robertocarrascoso/TeaTouch-CFGB_Las_Naves_Salesianos/Branding/adsadasdsad.png

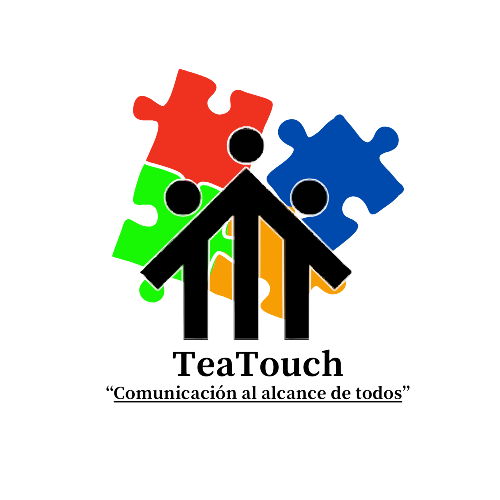
Branding/adsadasdsad.png
