robertocarrascoso/TeaTouch-CFGB_Las_Naves_Salesianos/Branding/asoc.-implica.jpg

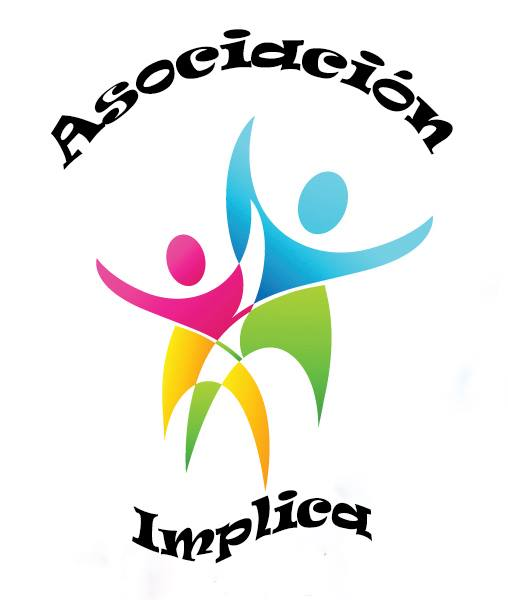
Branding/asoc.-implica.jpg
