robertocarrascoso/TeaTouch-CFGB_Las_Naves_Salesianos/Branding/asoc.-impplica.png

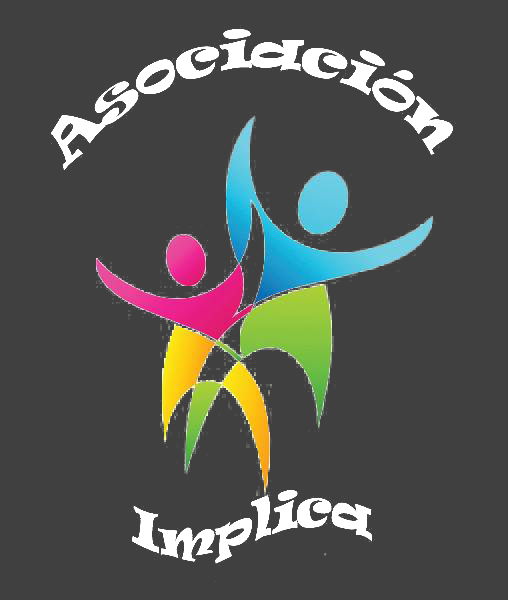
Branding/asoc.-impplica.png
