robertocarrascoso/TeaTouch-CFGB_Las_Naves_Salesianos/Branding/images.png

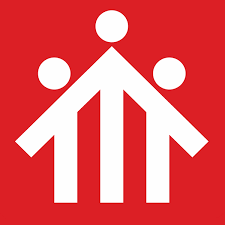
Branding/images.png
