robertocarrascoso/TeaTouch-CFGB_Las_Naves_Salesianos/Código y circuito/Circuito.png

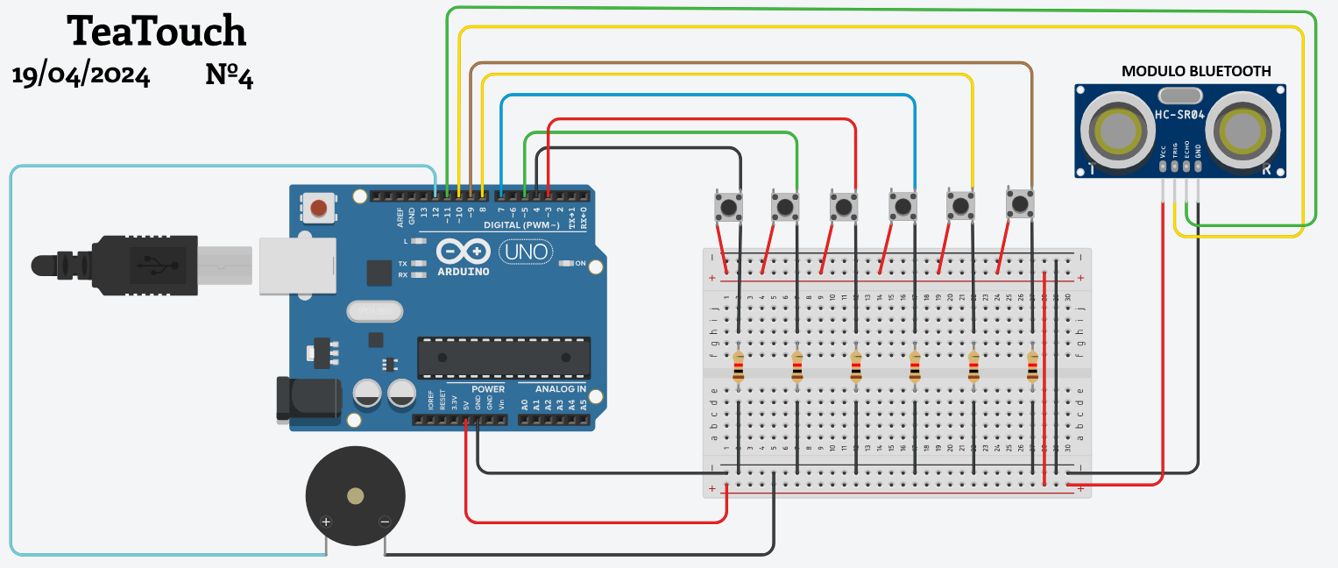
Código y circuito/Circuito.png
