robertocarrascoso/TeaTouch-CFGB_Las_Naves_Salesianos/Modelo 3D/2.png

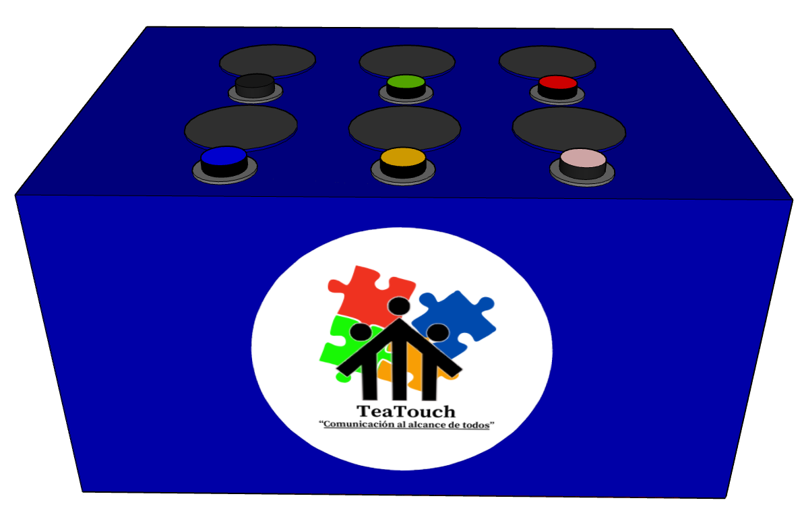
Modelo 3D/2.png
