robertocarrascoso/TeaTouch-CFGB_Las_Naves_Salesianos/Modelo 3D/bbbb.png

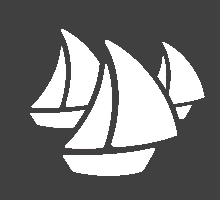
Modelo 3D/bbbb.png
