robertocarrascoso/TeaTouch-CFGB_Las_Naves_Salesianos/Pictogramas/pictograma_agua.png

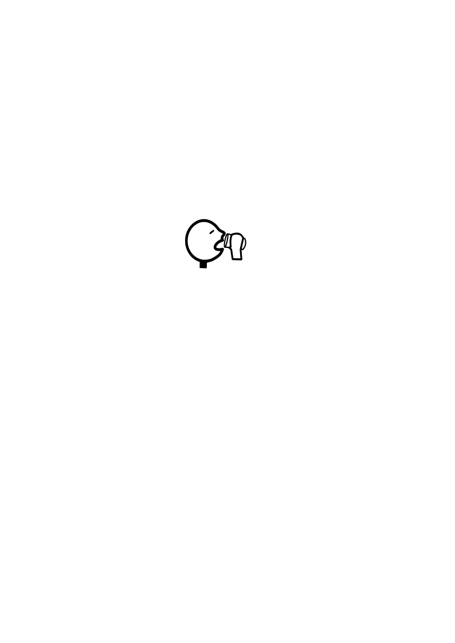
Pictogramas/pictograma_agua.png
