robertocarrascoso/TeaTouch-CFGB_Las_Naves_Salesianos/Pictogramas/pictograma_television.png

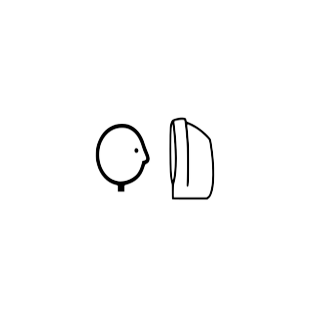
Pictogramas/pictograma_television.png
