robertocarrascoso/TeaTouch-CFGB_Las_Naves_Salesianos/Planos/A-plano 3.png

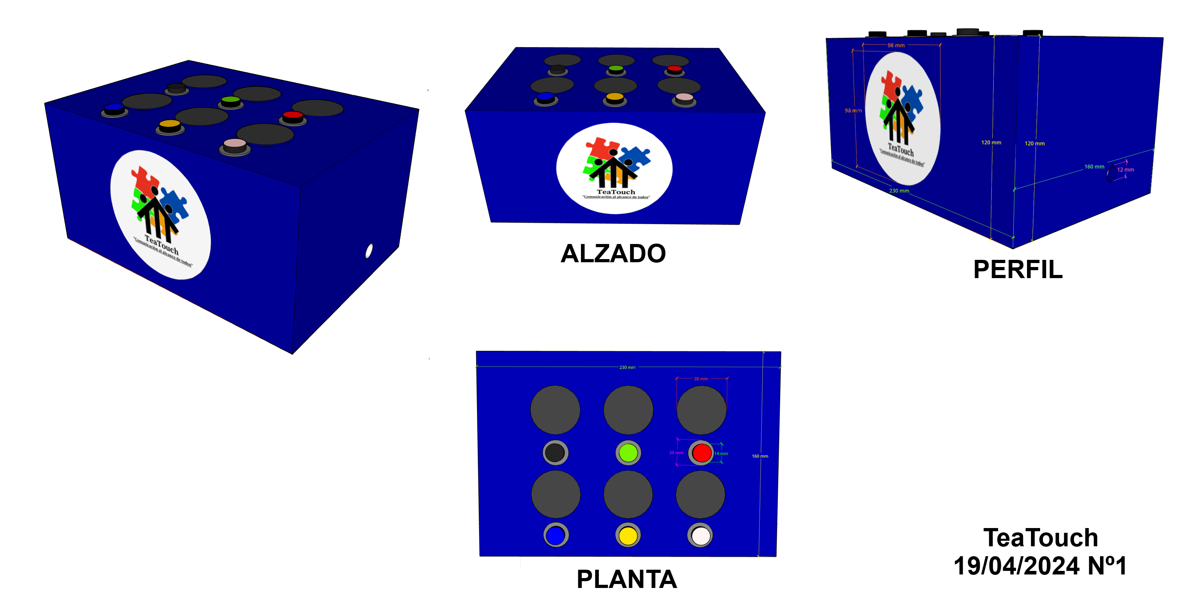
Planos/A-plano 3.png
