robertocarrascoso/TeaTouch-CFGB_Las_Naves_Salesianos/Planos/plano 1.png

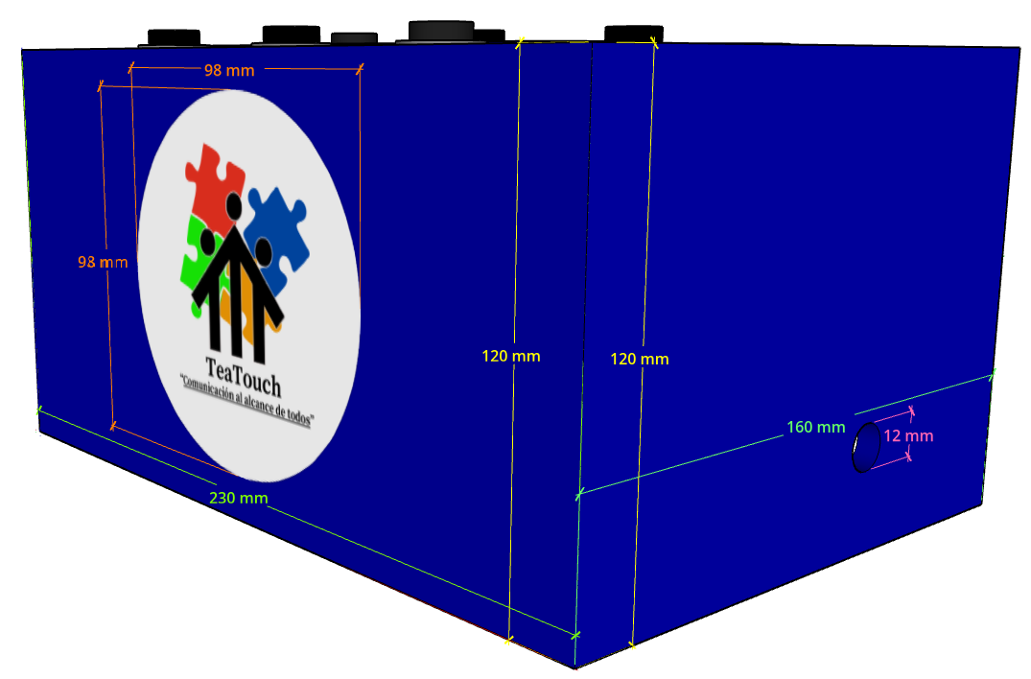
Planos/plano 1.png
