robertocarrascoso/TeaTouch-CFGB_Las_Naves_Salesianos/Planos/plano 2.png

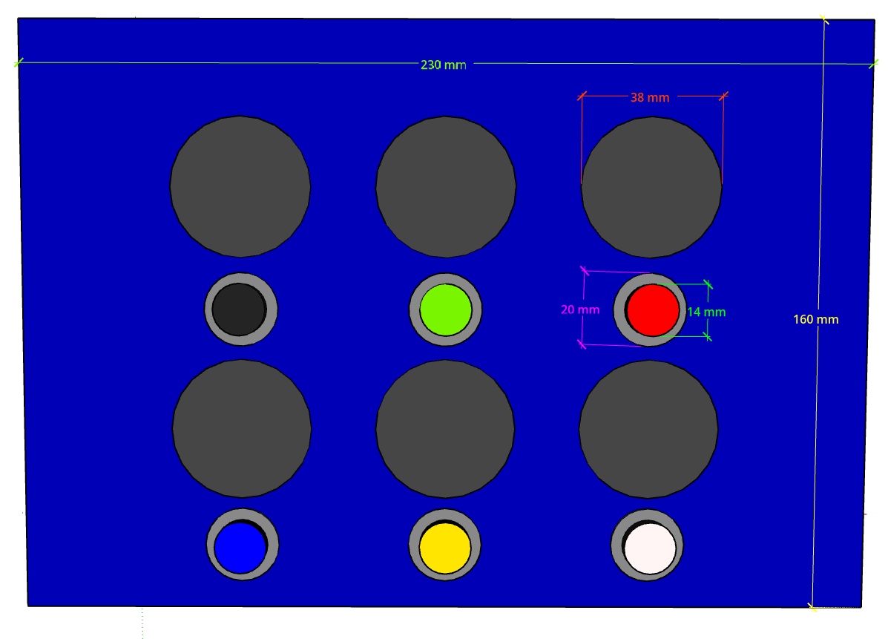
Planos/plano 2.png
